Joshua000977/Motorcycle-Notification-Display/FirmwareESPC3SuperMini/BikeNotifyDisplay/include/MySetup.h

#pragma once

#define GC9A01_DRIVER

#define TFT_WIDTH  240
#define TFT_HEIGHT 240

#define TFT_MOSI 7
#define TFT_SCLK 6
#define TFT_CS   10
#define TFT_DC   4
#define TFT_RST -1

#define TFT_RGB_ORDER TFT_RGB

#define LOAD_GLCD
#define LOAD_FONT2
#define LOAD_FONT4
#define LOAD_FONT6
#define LOAD_FONT7
#define LOAD_FONT8

#define SPI_FREQUENCY 10000000
